CalinRadoni/PAx5/SW/PAx5_Base/src/Board/cpu_USART1.h

/**
This file is part of PAx5 (https://github.com/CalinRadoni/PAx5)
Copyright (C) 2016, 2017 by Calin Radoni

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
You should have received a copy of the GNU General Public License
along with this program.  If not, see <http://www.gnu.org/licenses/>.
*/

#ifndef cpu_USART1_H_
#define cpu_USART1_H_

#include "MainBoard_Base.h"

namespace PAx5 {

const uint8_t U1_RX_BUFF_LEN = 64;
const uint8_t U1_TX_BUFF_LEN = 64;

class CPU_USART1 {
public:
	CPU_USART1();
	virtual ~CPU_USART1();

	volatile uint8_t bufferRX[U1_RX_BUFF_LEN];
	volatile uint8_t buffRxIdx;
	volatile bool    dataReceived;
	volatile bool	 dataOverflow;

	volatile bool    intfError;

	/**
	 * \brief Initialize this object's state
	 *
	 * \details This function is called by object's constructor
	 */
	void Initialize(void);

	/**
	 * \brief Compute #USARTDivider for requested baud rate and clock
	 *
	 * \details When oversampling by 16 #USARTDivider = #fck / #baudRate

	 * This function computes #USARTDivider, required for the #Configure function,
	 * and checks:
	 * - 0x10 <= #USARTDivider (required by RM0377 specification)
	 * - #USARTDivider <= 0xFFFF (required by RM0377 specification)
	 * - baud rate error < 3% (required by RM0377 specification)
	 *
	 * If the checks are not respected #USARTDivider will be set to 0 and the function
	 * will return false.
	 */
	bool ComputeUSARTDivider(uint32_t fck, uint32_t baudRate);

	/**
	 * \brief Configure the USART
	 *
	 * \details This function configure USART1 to user specified baud rate, 8N1, interrupt enabled
	 *
	 * \note Call #ComputeUSARTDivider function to compute #USARTDivider, required for configuration
	 *
	 * \return false if no idle frame is detected within defined timeout.
	 */
	bool Configure(void);

	void InitTxData(void);
	void AddTxData(uint8_t);
	uint8_t TxDataAvailableSpace(void);
	void SendTxData(void);
	void SendTxDataAndWait(void);
	bool DataIsSent(void);

	void ClearRXBuffer(void);

	void HandleInterrupt(void);

protected:
	volatile uint8_t bufferTX[U1_RX_BUFF_LEN];
	volatile uint8_t buffTxLen;
	volatile uint8_t buffTxIdx;
	volatile bool dataSent;

	uint32_t USARTDivider;
};

extern CPU_USART1 sUSART;

} /* namespace */
#endif /* cpu_USART1_H_ */
